tmnvanderberg/plants/context/BH1750 16bit Digital I2C Light Sensor Module - BH1750FVI_files/bh1750 mod 1-600x600.jpg

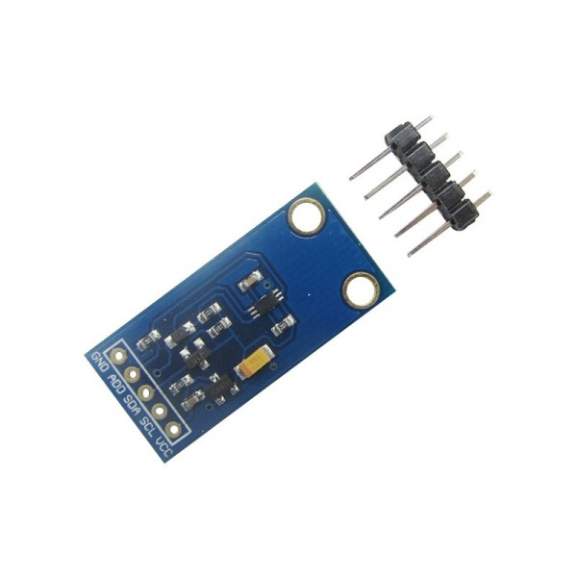
context/BH1750 16bit Digital I2C Light Sensor Module - BH1750FVI_files/bh1750 mod 1-600x600.jpg
