tmnvanderberg/plants/context/Capacitive Soil Moisture Sensor Module with Cable - SOILMOISWCABLE_files/capacitive-soil-moisture-sensor-module-with-cable-600x600.jpg

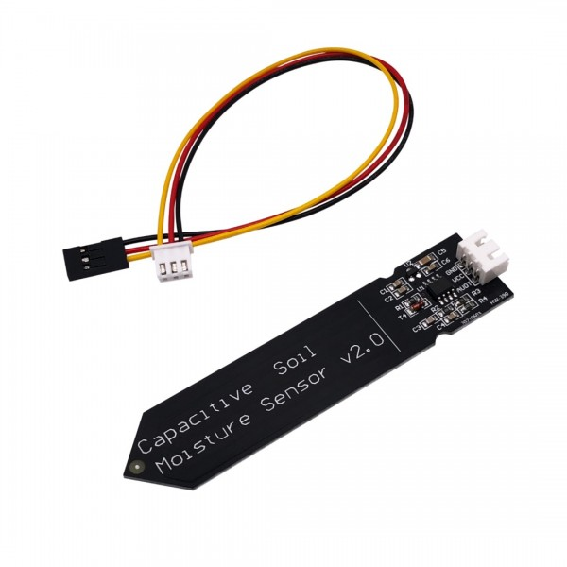
context/Capacitive Soil Moisture Sensor Module with Cable - SOILMOISWCABLE_files/capacitive-soil-moisture-sensor-module-with-cable-600x600.jpg
