tmnvanderberg/plants/hardware/carrier/carrier.kicad_sch

## KiCad design hardware/carrier/carrier.kicad_sch (2026-05-04)

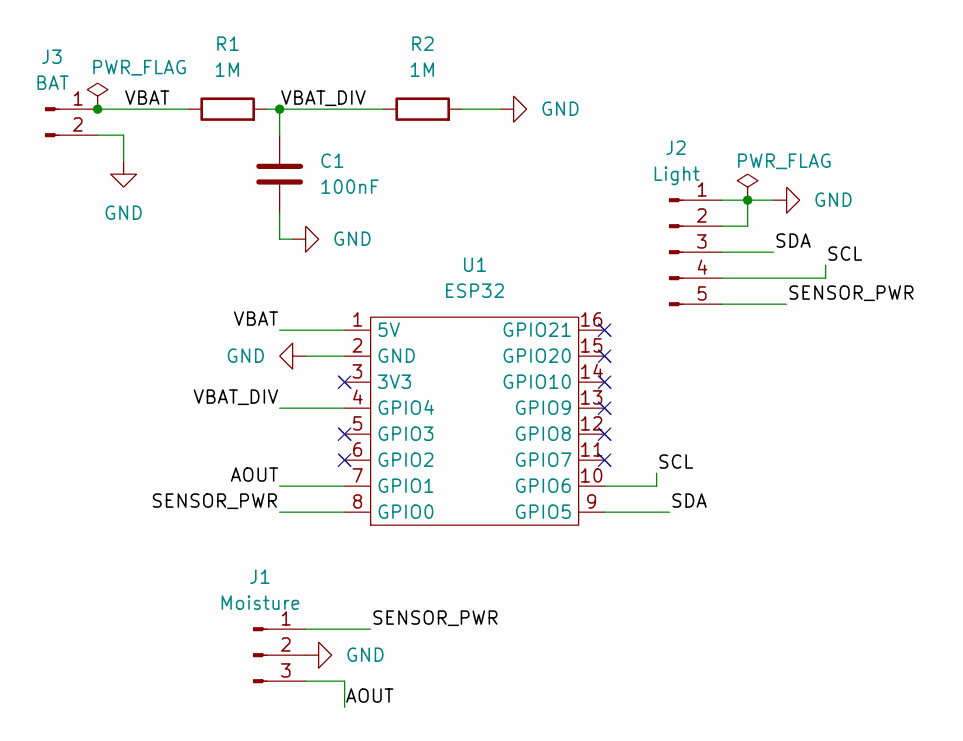
[picture p6: schematic carrier.kicad_sch]

Parts:
C1: 100nF
J1: Moisture
J2: Light
J3: BAT
R1, R2: 1M
U1: ESP32

Connections:
AOUT: J1.3, U1.7 (GPIO1)
GND: C1.2, J1.2, J2.1, J2.2, J3.2, R2.2, U1.2 (GND)
SCL: J2.4, U1.10 (GPIO6)
SDA: J2.3, U1.9 (GPIO5)
SENSOR_PWR: J1.1, J2.5, U1.8 (GPIO0)
VBAT: J3.1, R1.1, U1.1 (5V)
VBAT_DIV: C1.1, R1.2, R2.1, U1.4 (GPIO4)
